nickzswammer/ESP32-Clock-Gallery/Firmware/Combined/full_disp_AND_upload/AppState.h

#ifndef APP_STATE_H
#define APP_STATE_H

#include <Arduino.h>
#include <FS.h>

#define MAX_FILES 20
#define MAX_FILES_PER_PAGE 5
#define MAX_PAGES MAX_FILES/MAX_FILES_PER_PAGE // 20 / 5 = 4

#define MAX_FILENAME_LENGTH 200

struct AppState {
    // Button states
    int currButton1 = 1, prevButton1 = 0;
    int currButton2 = 1, prevButton2 = 0;
    int currButton3 = 1, prevButton3 = 0;
    int currButton4 = 1, prevButton4 = 0;
    int currALRT = 1, prevALRT = 0;
  
    // Display control
    bool fileMode = false; // file select mode or page increment mode
  
    // SD state
    bool sdPresent = false;
    File root;
    File currentFile;
    String currentFileName = "";
  
    // File indexing
    int currentFileIndex = 0;
    int currentPage = 0;
    int currentPageFile;
    int fileCount = MAX_FILES;
    String fileNames[MAX_PAGES][MAX_FILES_PER_PAGE]; // fileNames[4][5]
    int totalPages = 0;

  
    void resetButtons() {
      prevButton1 = currButton1;
      prevButton2 = currButton2;
      prevButton3 = currButton3;
      prevButton4 = currButton4;
    }
  
    bool wasPressed(int curr, int prev) {
      return (curr == LOW && prev == HIGH);
    }
  };

extern AppState app;

#endif
