nickzswammer/ESP32-Clock-Gallery/Firmware/Displays/OLED_Test/OLED_Test.ino

#include <Wire.h>
#include <Adafruit_GFX.h>
#include <Adafruit_SSD1306.h>

#define SCREEN_WIDTH 128
#define SCREEN_HEIGHT 64

Adafruit_SSD1306 display(SCREEN_WIDTH, SCREEN_HEIGHT, &Wire, -1);

uint8_t steph[] = {
  0x00,0x00,0x00,0x00,0x00,0x00,0x00,0x00,0x00,0x00,0x00,0x00,0x00,0x00,0x00,0x00,
  0x00,0x00,0x00,0x00,0x00,0x00,0x00,0x00,0x00,0x00,0x00,0x00,0x00,0x00,0x00,0x00,
  0x00,0x00,0x00,0x00,0x00,0x00,0x00,0x00,0x00,0x00,0x00,0x00,0x00,0x00,0x00,0x00,
  0x00,0x00,0x00,0x00,0x00,0x00,0x00,0x00,0x00,0x00,0x00,0x00,0x00,0x00,0x00,0x00,
  0x00,0x00,0x00,0x00,0x00,0x00,0x00,0x00,0x00,0x00,0x00,0x00,0x00,0x00,0x00,0x00,
  0x00,0x00,0x00,0x00,0x00,0x00,0x03,0xFF,0xFF,0xFE,0x00,0x00,0x00,0x00,0x00,0x00,
  0x00,0x00,0x00,0x00,0x00,0x03,0xFF,0xFF,0xFF,0xFF,0xF8,0x00,0x00,0x00,0x00,0x00,
  0x00,0x00,0x00,0x00,0x01,0xFF,0xFF,0xFF,0xFF,0xFF,0xFF,0x80,0x00,0x00,0x00,0x00,
  0x00,0x00,0x00,0x00,0x0F,0xFF,0xFF,0xFF,0xFF,0xFF,0xFF,0xFE,0x00,0x00,0x00,0x00,
  0x00,0x00,0x00,0x01,0xFF,0xFF,0xFF,0xFF,0xFF,0xFF,0xFF,0xFF,0xC0,0x00,0x00,0x00,
  0x00,0x00,0x00,0x0F,0xFF,0xFF,0xFF,0xFF,0xFF,0xFF,0xFF,0xFF,0xFC,0x00,0x00,0x00,
  0x00,0x00,0x00,0x7F,0xFF,0xFF,0xFF,0xFF,0xFF,0xFF,0xFF,0xFF,0xFF,0x00,0x00,0x00,
  0x00,0x00,0x00,0xFF,0xFF,0xFF,0xFF,0xFF,0xFF,0xFF,0xFF,0xFF,0xFF,0xC0,0x00,0x00,
  0x00,0x00,0x03,0xFF,0xFF,0xFF,0xFF,0xFF,0xFF,0xFF,0xFF,0xFF,0xFF,0xF0,0x00,0x00,
  0x00,0x00,0x07,0xFF,0xFF,0xFF,0xFF,0xFF,0xFF,0xFF,0xFF,0xFF,0xFF,0xF8,0x00,0x00,
  0x00,0x00,0x0F,0xFF,0xE0,0x00,0x00,0x10,0x47,0xFF,0xFF,0xFF,0xFF,0xFC,0x00,0x00,
  0x00,0x00,0x0F,0xFF,0x80,0x00,0x00,0x00,0x00,0x00,0x00,0x7F,0xFF,0xFC,0x00,0x00,
  0x00,0x00,0x1F,0xFE,0x00,0x00,0x00,0x00,0x00,0x00,0x00,0x01,0xFF,0xFE,0x00,0x00,
  0x00,0x00,0x1F,0xF8,0x00,0x00,0x00,0x00,0x00,0x00,0x00,0x00,0x7F,0xFE,0x00,0x00,
  0x00,0x00,0x1F,0xF0,0x00,0xFC,0x00,0x00,0x00,0x00,0x00,0x00,0x7F,0xFE,0x00,0x00,
  0x00,0x00,0x1F,0xE0,0x03,0xC0,0x00,0x00,0x00,0x00,0x00,0x00,0x3F,0xFE,0x00,0x00,
  0x00,0x00,0x1F,0xC0,0x00,0x00,0x00,0x00,0x00,0x00,0x00,0x00,0x03,0xFE,0x00,0x00,
  0x00,0x00,0x3F,0x80,0x00,0x00,0x00,0x00,0x00,0x00,0x00,0x00,0x03,0xFE,0x00,0x00,
  0x00,0x00,0x1F,0x80,0x00,0x00,0x00,0x00,0x00,0x00,0x00,0x00,0x03,0xFC,0x00,0x00,
  0x00,0x00,0x3F,0x00,0x00,0x00,0x00,0x00,0x00,0x00,0x00,0x00,0x07,0xFC,0x00,0x00,
  0x00,0x00,0x3F,0x00,0x00,0x00,0x00,0x00,0x00,0x00,0x00,0x00,0x07,0xF8,0x00,0x00,
  0x00,0x00,0x1E,0x00,0x00,0x00,0x00,0x00,0x00,0x00,0x00,0x00,0x5F,0xF8,0x00,0x00,
  0x00,0x00,0x1F,0x00,0x03,0xFF,0xF8,0x00,0x00,0x07,0x48,0x00,0x21,0xF0,0x00,0x00,
  0x00,0x00,0x0F,0x00,0xFF,0xFF,0xFF,0x80,0x67,0xFF,0xFF,0x80,0x07,0xF0,0x00,0x00,
  0x00,0x00,0x87,0x00,0x0F,0xFF,0xFF,0x80,0xFF,0xFF,0xFF,0xFC,0x03,0xF0,0x00,0x00,
  0x00,0x01,0xC2,0x00,0x7F,0xFF,0xFF,0x00,0x3F,0xFF,0xFF,0xFE,0x03,0xE0,0x40,0x00,
  0x00,0x01,0x80,0x03,0xFF,0x1F,0xFF,0x80,0x3F,0xFF,0xFF,0xFF,0x00,0xDF,0x80,0x00,
  0x00,0x00,0x00,0x00,0x00,0x0F,0xFD,0x80,0x1F,0xFF,0xFF,0xFF,0x00,0xFF,0xC0,0x00,
  0x00,0x00,0x78,0x00,0x01,0xFF,0xFC,0x00,0x0F,0xFF,0xFF,0xFF,0x00,0xFC,0xC0,0x00,
  0x00,0x00,0x60,0x00,0x00,0x00,0x00,0x00,0x03,0xFF,0xFF,0x00,0x00,0xFF,0x00,0x00,
  0x00,0x00,0x00,0x00,0x00,0x00,0x00,0x00,0x01,0x00,0x00,0x00,0x00,0x3F,0x00,0x00,
  0x00,0x00,0x00,0x00,0x00,0x00,0x00,0x00,0x00,0x00,0x00,0x00,0x01,0xBC,0x00,0x00,
  0x00,0x00,0x00,0x00,0x00,0x00,0x00,0x00,0x00,0x00,0x00,0x00,0x01,0xE5,0x00,0x00,
  0x00,0x00,0x01,0x00,0x00,0x00,0x00,0x00,0x00,0x30,0x00,0x00,0x02,0x00,0x00,0x00,
  0x00,0x00,0x00,0x00,0x00,0x7C,0x0F,0xDF,0xFF,0xFC,0x00,0x00,0x07,0xF0,0x00,0x00,
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
};

void setup() {
  Serial.begin(115200);
  if(!display.begin(SSD1306_SWITCHCAPVCC, 0x3C)) {
    Serial.println("SSD1306 allocation failed");
    for(;;);
  }

  delay(1000);

  display.clearDisplay();
  display.drawBitmap(0, 0, steph, 128, 64, 1);
  display.display();
}

void loop() {}
